OpenModbus/OM-16LED/kicad/OM-16LED.kicad_sch

## KiCad design kicad/OM-16LED.kicad_sch (2026-03-12)

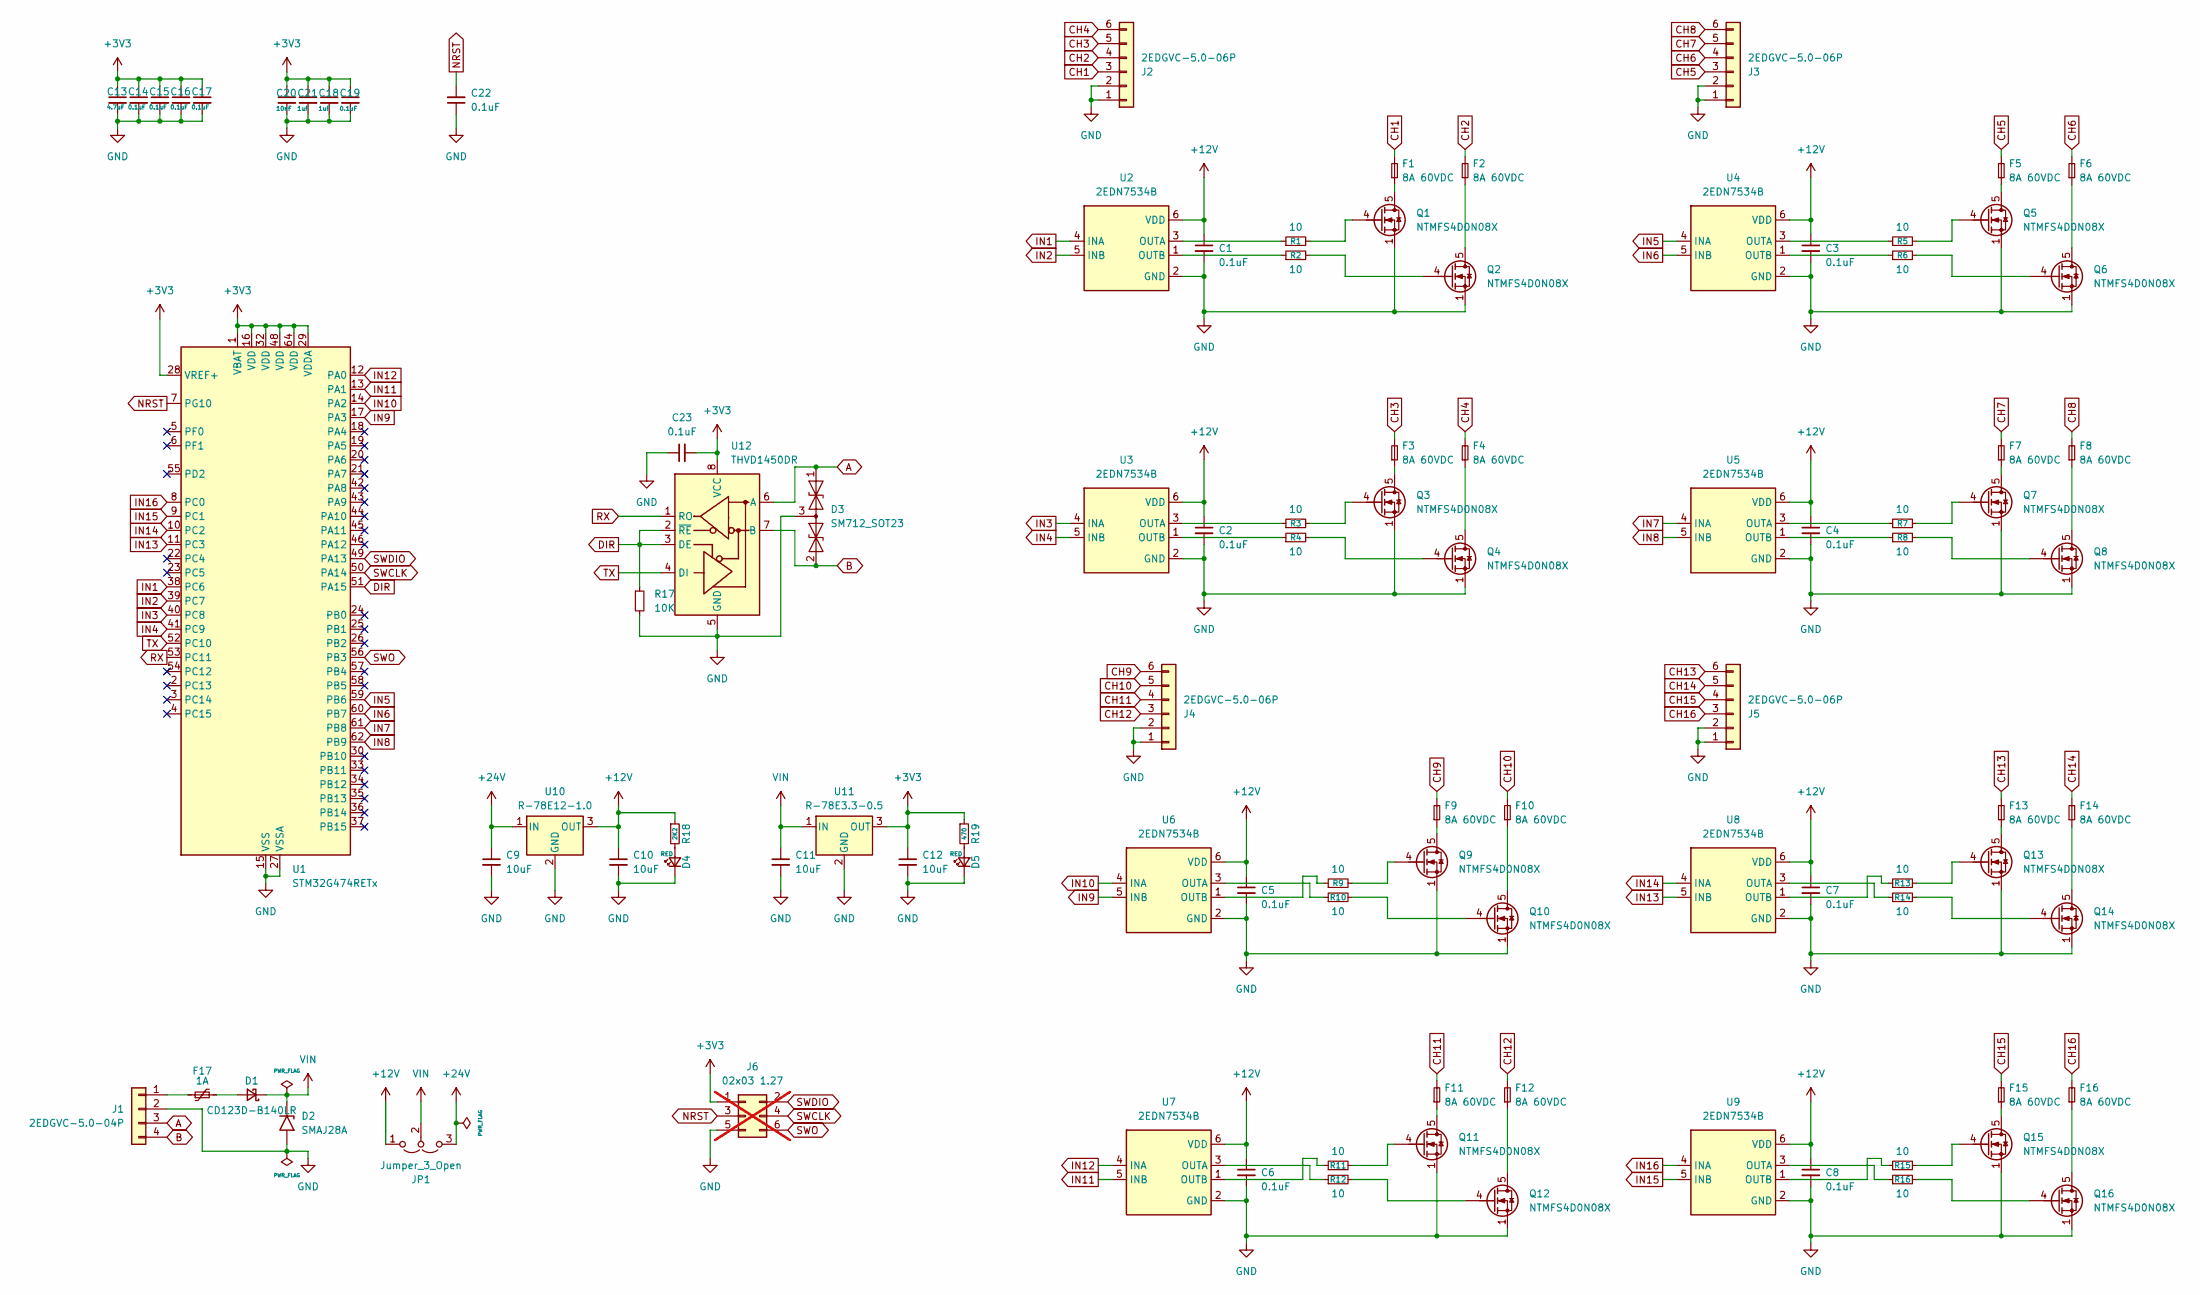
[picture p11: schematic OM-16LED.kicad_sch]

Parts:
C1, C2, C3, C4, C5, C6, C7, C8: 0.1uF; C_0805_2012Metric; Mouser# 81-GRT21BR71H104KE1L; LCSC# C782178
C9, C10, C11, C12: 10uF; C_1206_3216Metric; Mouser# 81-GRT31CR61H106KE1L; LCSC# C417124
C13: 4.7uF; C_0603_1608Metric; Mouser# 81-GRM188R61E475KE1D; LCSC# C90057
C14, C15, C16, C17, C19, C22, C23: 0.1uF; C_0603_1608Metric; Mouser# 81-GCJ188R71H104KA2D; LCSC# C161115
C18, C21: 1uF; C_0603_1608Metric; Mouser# 81-GRT188R61H105KE3D; LCSC# C126631
C20: 10nF; C_0603_1608Metric; Mouser# 81-GCM188R71H103KA7D; LCSC# C85863
D1: CD123D-B140LR; D_SOD-123; Mouser# 652-CD123D-B140LR; LCSC# C6877135
D2: SMAJ28A; D_SMA; Mouser# 576-SMAJ28A; LCSC# C148227
D3: SM712_SOT23; SOT-23; Mouser# 576-SM712-02HTG; LCSC# C172881
D4, D5: RED; LED_0603_1608Metric; Part Number LTST-C190EKT; LCSC# C364560
F1, F2, F3, F4, F5, F6, F7, F8, F9, F10, F11, F12, F13, F14, F15, F16: 8A 60VDC; Fuse_0679H; Mouser# 530-0679H8000-05; LCSC# C3156889
F17: 1A; Fuse_1206_3216Metric; Mouser# 576-0466001.NR; LCSC# C151135
J1: 2EDGVC-5.0-04P; TerminalBlock_DEGSON_2EDGVC-5.0-04P_No_SilkScreen; Part Number 10030002303; LCSC# C441377
J2, J3, J4, J5: 2EDGVC-5.0-06P; TerminalBlock_DEGSON_2EDGVC-5.0-06P_No_SilkScreen; Part Number 10030002306; LCSC# C441379
J6: 02x03 1.27; PinHeader_2x03_P1.27mm_Vertical; not fitted
JP1: Jumper_3_Open; PinHeader_1x03_P2.54mm_Vertical
Q1, Q2, Q3, Q4, Q5, Q6, Q7, Q8, Q9, Q10, Q11, Q12, Q13, Q14, Q15, Q16: NTMFS4D0N08X; ONSemi_SO-8FL_488AA; Mouser# 863-NTMFS4D0N08XT1G; LCSC# C35185549
R1, R2, R3, R4, R5, R6, R7, R8, R9, R10, R11, R12, R13, R14, R15, R16: 10; R_0603_1608Metric; Mouser# 667-ERJ-H3EF10R0V; LCSC# C2842424
R17: 10K; R_0603_1608Metric; Mouser# 667-ERJ-H3EF1002V; LCSC# C4297913
R18: 2K2; R_0603_1608Metric; Part Number ERJ-UP3J222V; LCSC# C491201
R19: 470; R_0603_1608Metric; Part Number ERJ-UP3J471V; LCSC# C491199
U1: STM32G474RETx; LQFP-64_10x10mm_P0.5mm; Mouser# 511-STM32G474RET6; LCSC# C521608
U2, U3, U4, U5, U6, U7, U8, U9: 2EDN7534B; SOT-23-6; Mouser# 726-2EDN7534BXTSA1; LCSC# C3654924
U10: R-78E12-1.0; Converter_DCDC_RECOM_R-78E-0.5_THT; Mouser# 919-R-78E12-1.0/X9; LCSC# C5240945
U11: R-78E3.3-0.5; Converter_DCDC_RECOM_R-78E-0.5_THT; Mouser# 919-R-78E3.3-0.5; LCSC# C18212316
U12: THVD1450DR; VSON-8-1EP_3x3mm_P0.65mm_EP1.6x2.4mm; Mouser# 595-THVD1450DRBR; LCSC# C1850226

Connections:
+3V3: C12.1, C13.1, C14.1, C15.1, C16.1, C17.1, C18.1, C19.1, C20.1, C21.1, C23.2, J6.1, R19.1, U1.1 (VBAT), U1.16 (VDD), U1.28 (VREF+), U1.29 (VDDA), U1.32 (VDD), U1.48 (VDD), U1.64 (VDD), U11.3 (OUT), U12.8 (VCC)
+12V: C1.1, C2.1, C3.1, C4.1, C5.1, C6.1, C7.1, C8.1, C10.1, JP1.1 (A), R18.1, U2.6 (VDD), U3.6 (VDD), U4.6 (VDD), U5.6 (VDD), U6.6 (VDD), U7.6 (VDD), U8.6 (VDD), U9.6 (VDD), U10.3 (OUT)
+24V: C9.1, JP1.3 (B), U10.1 (IN)
A: D3.1 (A1), J1.3, U12.6 (A)
B: D3.2 (A2), J1.4, U12.7 (B)
CH1: F1.2, J2.3
CH2: F2.2, J2.4
CH3: F3.2, J2.5
CH4: F4.2, J2.6
CH5: F5.2, J3.3
CH6: F6.2, J3.4
CH7: F7.2, J3.5
CH8: F8.2, J3.6
CH9: F9.2, J4.6
CH10: F10.2, J4.5
CH11: F11.2, J4.4
CH12: F12.2, J4.3
CH13: F13.2, J5.6
CH14: F14.2, J5.5
CH15: F15.2, J5.4
CH16: F16.2, J5.3
DIR: R17.1, U1.51 (PA15), U12.2 (~RE), U12.3 (DE)
GND: C1.2, C2.2, C3.2, C4.2, C5.2, C6.2, C7.2, C8.2, C9.2, C10.2, C11.2, C12.2, C13.2, C14.2, C15.2, C16.2, C17.2, C18.2, C19.2, C20.2, C21.2, C22.1, C23.1, D2.2 (A2), D3.3 (common), D4.1 (K), D5.1 (K), J1.2, J2.1, J2.2, J3.1, J3.2, J4.1, J4.2, J5.1, J5.2, J6.5, Q1.1 (S), Q1.2 (S), Q1.3 (S), Q2.1 (S), Q2.2 (S), Q2.3 (S), Q3.1 (S), Q3.2 (S), Q3.3 (S), Q4.1 (S), Q4.2 (S), Q4.3 (S), Q5.1 (S), Q5.2 (S), Q5.3 (S), Q6.1 (S), Q6.2 (S), Q6.3 (S), Q7.1 (S), Q7.2 (S), Q7.3 (S), Q8.1 (S), Q8.2 (S), Q8.3 (S), Q9.1 (S), Q9.2 (S), Q9.3 (S), Q10.1 (S), Q10.2 (S), Q10.3 (S), Q11.1 (S), Q11.2 (S), Q11.3 (S), Q12.1 (S), Q12.2 (S), Q12.3 (S), Q13.1 (S), Q13.2 (S), Q13.3 (S), Q14.1 (S), Q14.2 (S), Q14.3 (S), Q15.1 (S), Q15.2 (S), Q15.3 (S), Q16.1 (S), Q16.2 (S), Q16.3 (S), R17.2, U1.15 (VSS), U1.27 (VSSA), U1.31 (VSS), U1.47 (VSS), U1.63 (VSS), U2.2 (GND), U3.2 (GND), U4.2 (GND), U5.2 (GND), U6.2 (GND), U7.2 (GND), U8.2 (GND), U9.2 (GND), U10.2 (GND), U11.2 (GND), U12.5 (GND), U12.9 (GND)
IN1: U1.38 (PC6), U2.4 (INA)
IN2: U1.39 (PC7), U2.5 (INB)
IN3: U1.40 (PC8), U3.4 (INA)
IN4: U1.41 (PC9), U3.5 (INB)
IN5: U1.59 (PB6), U4.4 (INA)
IN6: U1.60 (PB7), U4.5 (INB)
IN7: U1.61 (PB8), U5.4 (INA)
IN8: U1.62 (PB9), U5.5 (INB)
IN9: U1.17 (PA3), U6.5 (INB)
IN10: U1.14 (PA2), U6.4 (INA)
IN11: U1.13 (PA1), U7.5 (INB)
IN12: U1.12 (PA0), U7.4 (INA)
IN13: U1.11 (PC3), U8.5 (INB)
IN14: U1.10 (PC2), U8.4 (INA)
IN15: U1.9 (PC1), U9.5 (INB)
IN16: U1.8 (PC0), U9.4 (INA)
NRST: C22.2, J6.3, U1.7 (PG10)
unnamed: D1.2 (A), F17.2
unnamed: D4.2 (A), R18.2
unnamed: D5.2 (A), R19.2
unnamed: F1.1, Q1.5 (D)
unnamed: F2.1, Q2.5 (D)
unnamed: F3.1, Q3.5 (D)
unnamed: F4.1, Q4.5 (D)
unnamed: F5.1, Q5.5 (D)
unnamed: F6.1, Q6.5 (D)
unnamed: F7.1, Q7.5 (D)
unnamed: F8.1, Q8.5 (D)
unnamed: F9.1, Q9.5 (D)
unnamed: F10.1, Q10.5 (D)
unnamed: F11.1, Q11.5 (D)
unnamed: F12.1, Q12.5 (D)
unnamed: F13.1, Q13.5 (D)
unnamed: F14.1, Q14.5 (D)
unnamed: F15.1, Q15.5 (D)
unnamed: F16.1, Q16.5 (D)
unnamed: F17.1, J1.1
unnamed: Q1.4 (G), R1.2
unnamed: Q2.4 (G), R2.2
unnamed: Q3.4 (G), R3.2
unnamed: Q4.4 (G), R4.2
unnamed: Q5.4 (G), R5.2
unnamed: Q6.4 (G), R6.2
unnamed: Q7.4 (G), R7.2
unnamed: Q8.4 (G), R8.2
unnamed: Q9.4 (G), R9.2
unnamed: Q10.4 (G), R10.2
unnamed: Q11.4 (G), R11.2
unnamed: Q12.4 (G), R12.2
unnamed: Q13.4 (G), R13.2
unnamed: Q14.4 (G), R14.2
unnamed: Q15.4 (G), R15.2
unnamed: Q16.4 (G), R16.2
unnamed: R1.1, U2.3 (OUTA)
unnamed: R2.1, U2.1 (OUTB)
unnamed: R3.1, U3.3 (OUTA)
unnamed: R4.1, U3.1 (OUTB)
unnamed: R5.1, U4.3 (OUTA)
unnamed: R6.1, U4.1 (OUTB)
unnamed: R7.1, U5.3 (OUTA)
unnamed: R8.1, U5.1 (OUTB)
unnamed: R9.1, U6.1 (OUTB)
unnamed: R10.1, U6.3 (OUTA)
unnamed: R11.1, U7.1 (OUTB)
unnamed: R12.1, U7.3 (OUTA)
unnamed: R13.1, U8.1 (OUTB)
unnamed: R14.1, U8.3 (OUTA)
unnamed: R15.1, U9.1 (OUTB)
unnamed: R16.1, U9.3 (OUTA)
RX: U1.53 (PC11), U12.1 (RO)
SWCLK: J6.4, U1.50 (PA14)
SWDIO: J6.2, U1.49 (PA13)
SWO: J6.6, U1.56 (PB3)
TX: U1.52 (PC10), U12.4 (DI)
VIN: C11.1, D1.1 (K), D2.1 (A1), JP1.2 (C), U11.1 (IN)
